EDD2526/edd-project-grup-dijous-dj_a_combustible/DIAGRAMA BLOCS/diagramaBLOCS_160326.png

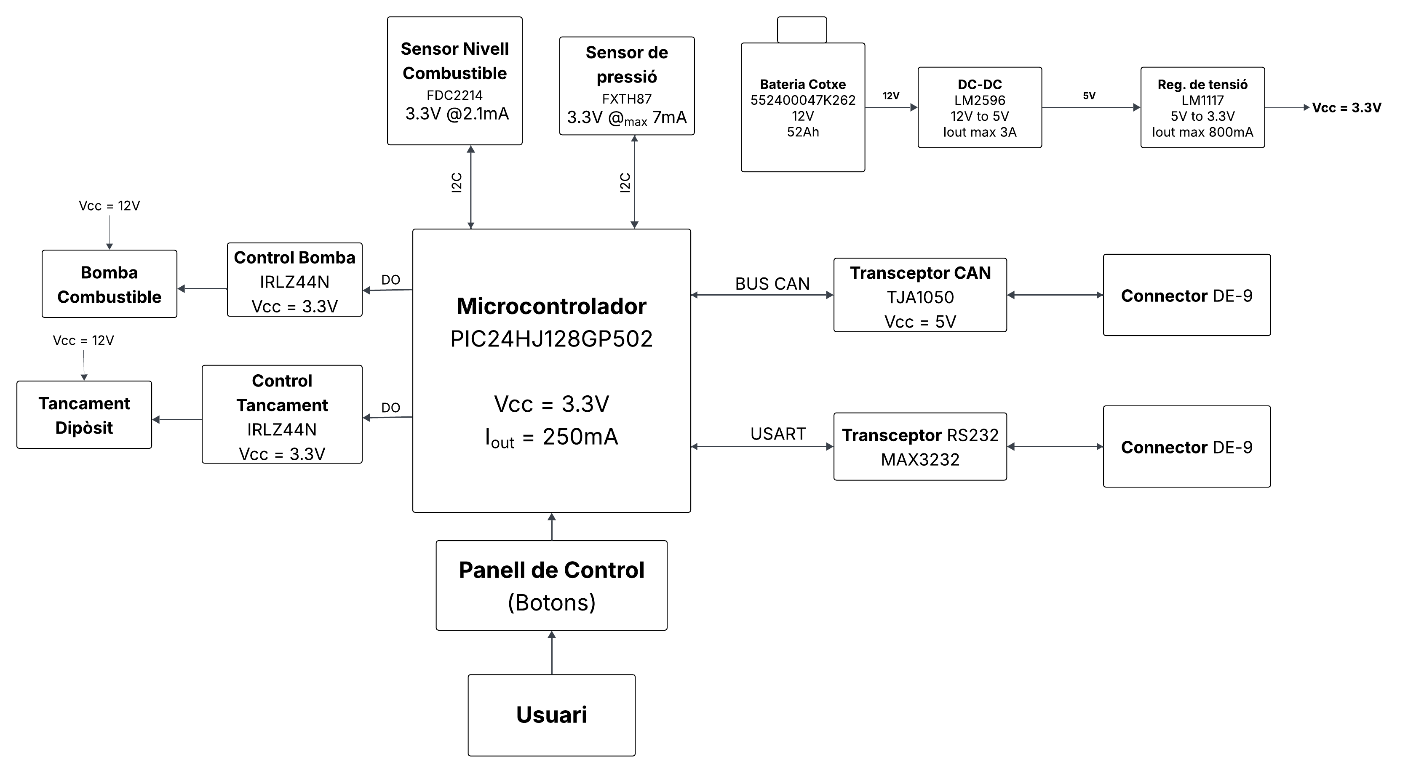
DIAGRAMA BLOCS/diagramaBLOCS_160326.png
