EDD2526/edd-project-grup-dijous-dj_a_combustible/DIAGRAMA BLOCS/diagramaBlocs_etapa3_millorada.png

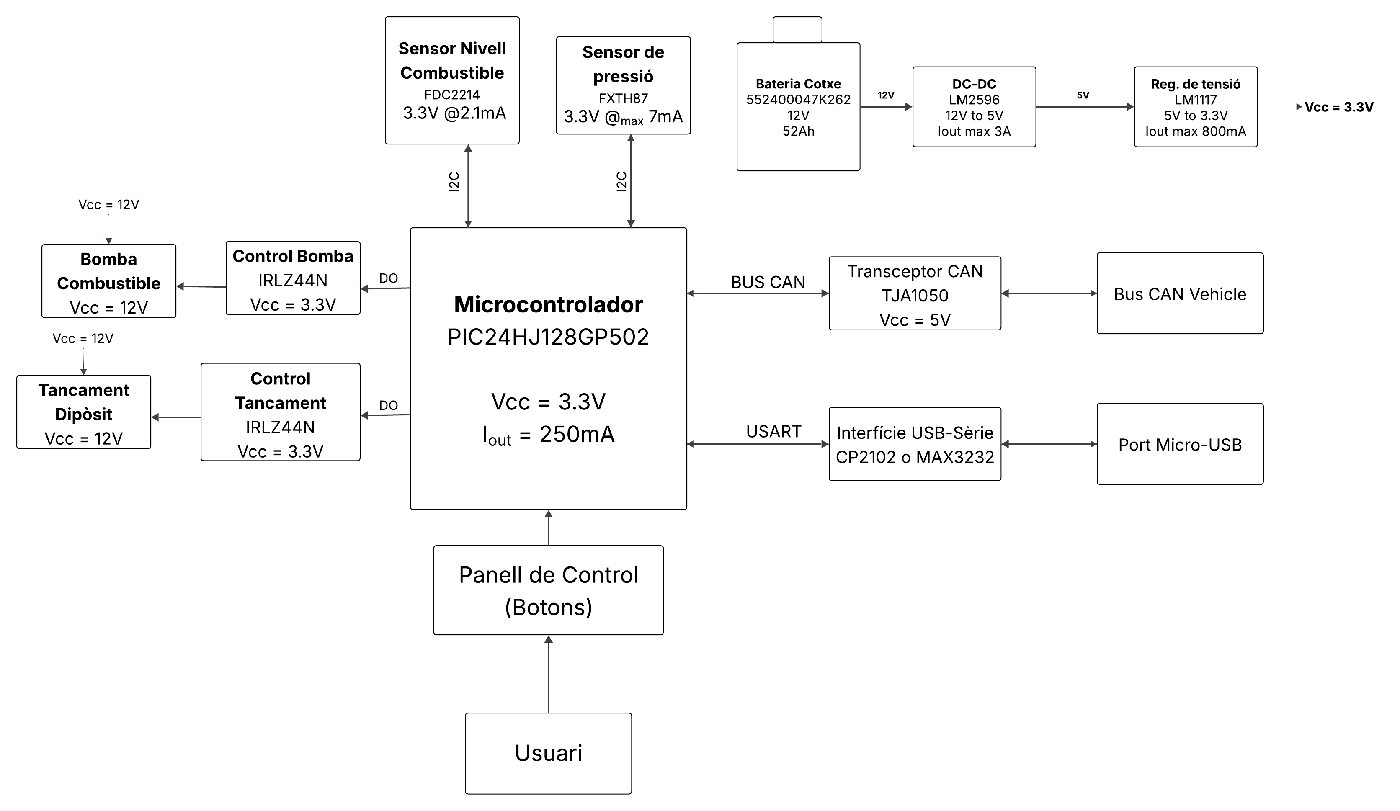
DIAGRAMA BLOCS/diagramaBlocs_etapa3_millorada.png
