EDD2526/edd-project-grup-dijous-dj_a_combustible/DIAGRAMA BLOCS/quasifinaldiagrama.png

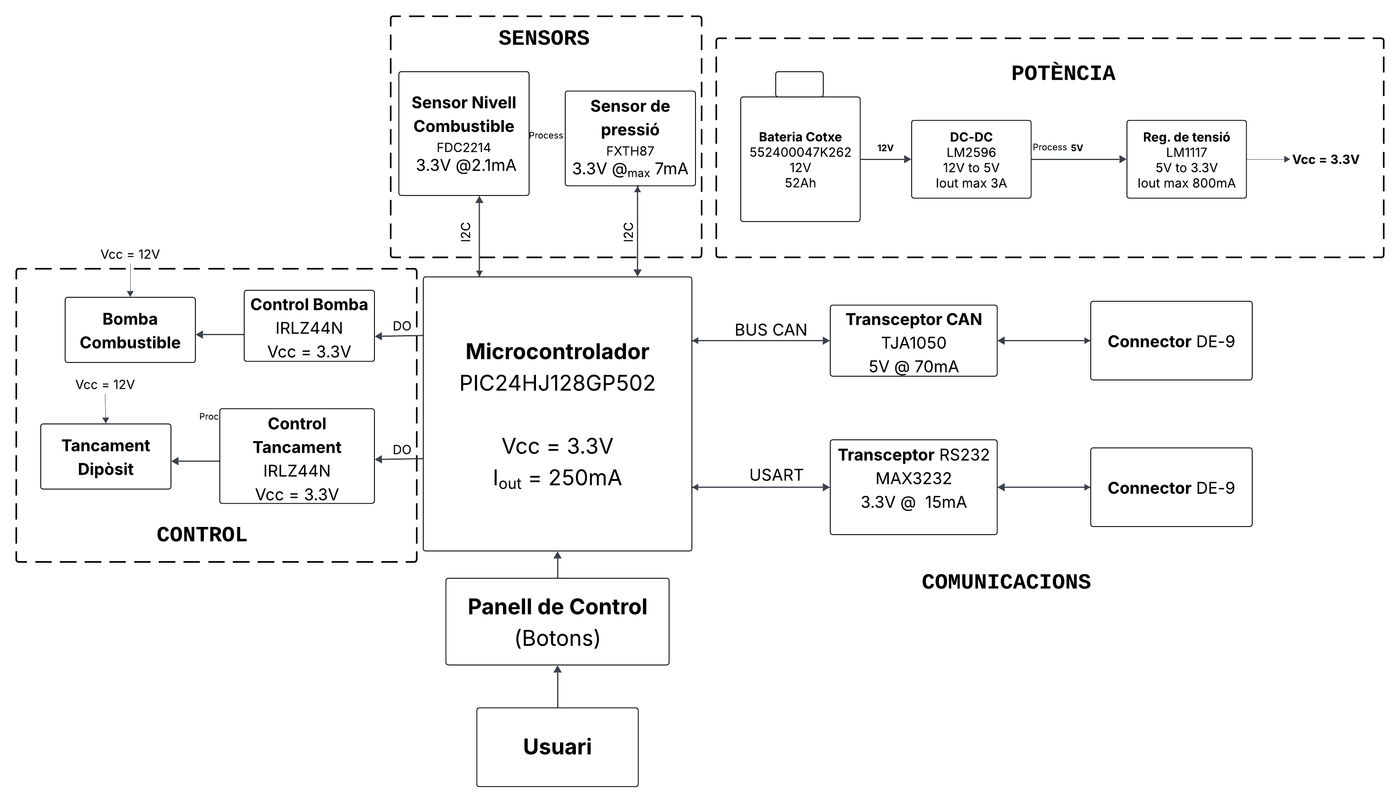
DIAGRAMA BLOCS/quasifinaldiagrama.png
