EDD2526/edd-project-grup-dijous-dj_a_combustible/Layout/AA_drcpassatFINAL.png

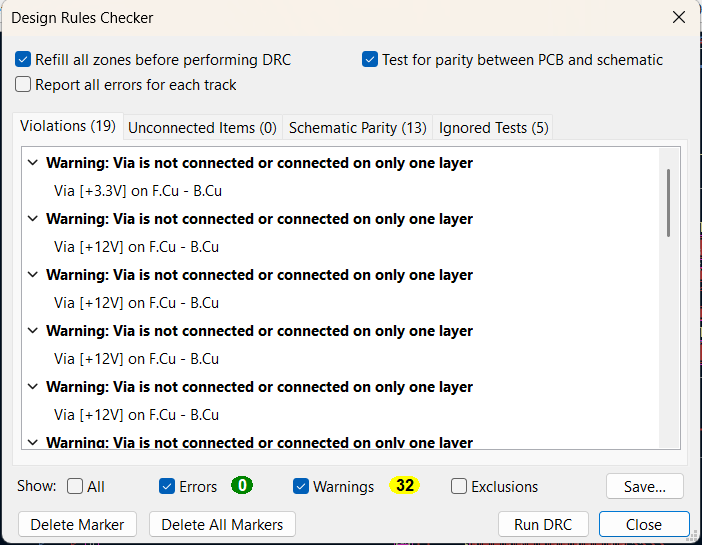
Layout/AA_drcpassatFINAL.png
