EDD2526/edd-project-grup-dijous-dj_a_combustible/Layout/AA_layout3D_bottom.png

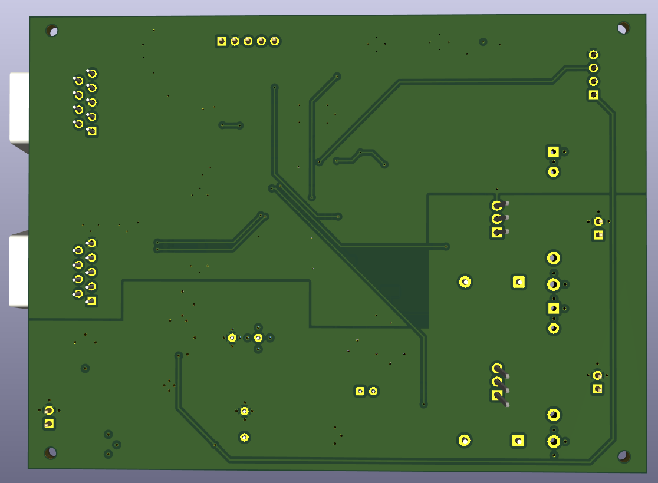
Layout/AA_layout3D_bottom.png
