EDD2526/edd-project-grup-dijous-dj_a_combustible/Layout/layout3D_v2.png

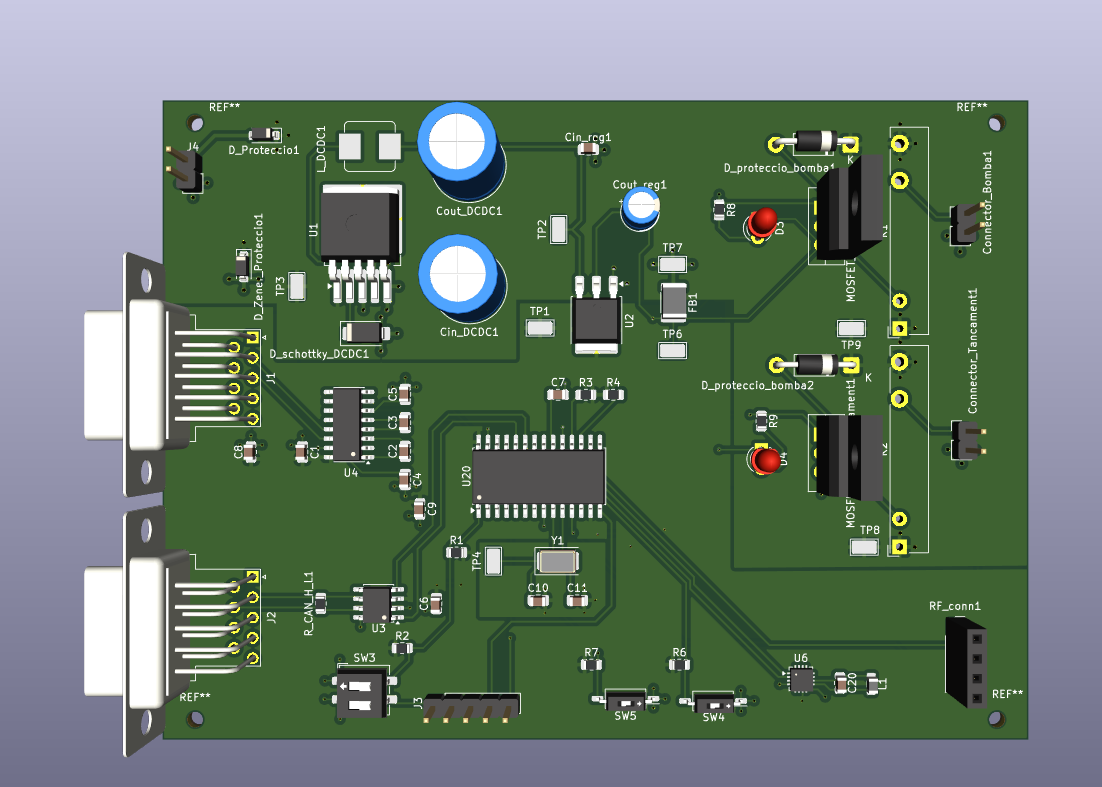
Layout/layout3D_v2.png
