EDD2526/edd-project-grup-dijous-dj_a_combustible/Layout/Routing v1.png

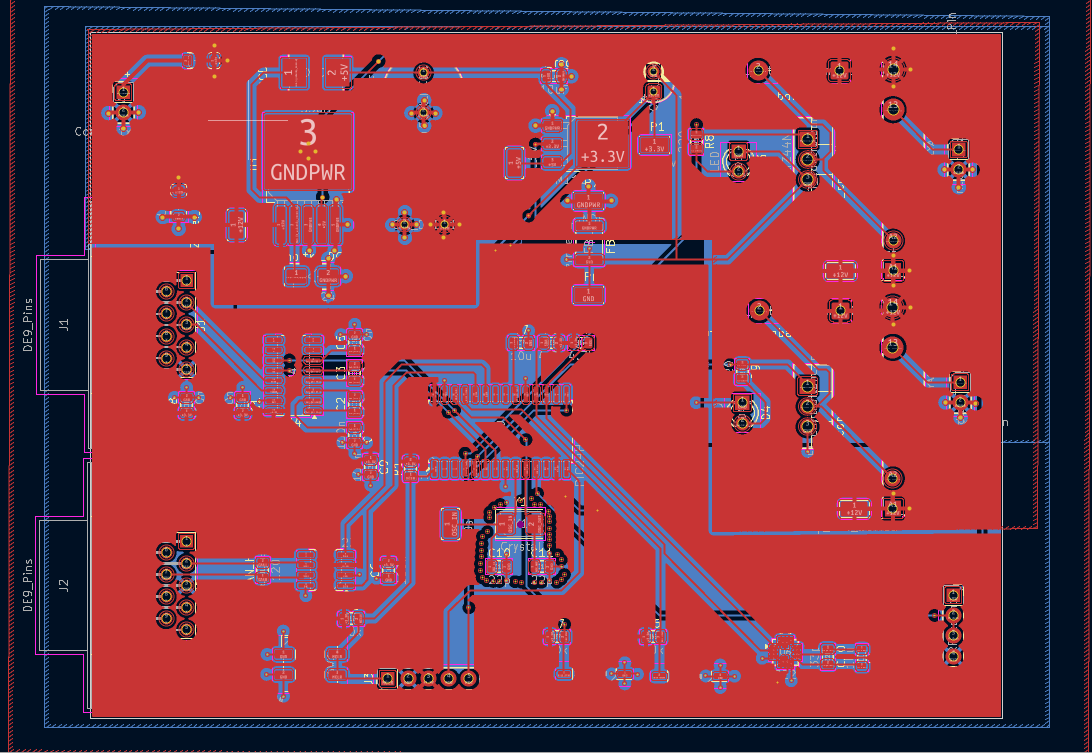
Layout/Routing v1.png
