EDD2526/edd-project-grup-dijous-dj_a_combustible/LTspice_simulations/control_MOSFET&RELE.asc

L1: ind; 100m; Rser=400
M1: nmos; alfredpapi
R1: res; 30
S1: sw; rele
V1: voltage; PULSE(0 3.3 1m 1u 1u 10m 20m)
V2: voltage; 12
V3: voltage; 12
Named nets: 0, Digital_Output, Node_Motor
.tran 100m
.model alfredpapi VDMOS(Rg=3 Vto=1.5 Rd=0.1 Rs=0.1 Rb=0.05 Kp=5 Cgs=50p Cgd=10p)
.model rele SW(Vt=6 Vh=1 Ron=0.1 Roff=1G)
