EDD2526/edd-project-grup-dijous-dj_a_combustible/LTspice_simulations/control_MOSFETs.asc

M1: nmos; alfredpapi
R1: res; 30
V1: voltage; PULSE(0 3.3 1m 1u 1u 10m 20m)
V2: voltage; 12
Named nets: 0
.tran 100m
.model alfredpapi VDMOS(Rg=3 Vto=1.5 Rd=0.1 Rs=0.1 Rb=0.05 Kp=5 Cgs=50p Cgd=10p)
